michar71/DMX_CTRL/SW/Inc/WS2812B.h

#ifndef WS2812B_H
#define WS2812B_H

#include <stdio.h>
#include <string.h>
#include <stdarg.h>

// New version uses one large LUT as its faster index into sequential bytes for the GRB pattern
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
uint8_t rOffset;       // Index of red byte within each 3- or 4-byte pixel
uint8_t gOffset;       // Index of green byte
uint8_t bOffset;       // Index of blue byte

#endif // WS2812B_H
