michar71/DMX_CTRL/SW/Inc/serial_dmx_parser.h

/*
 * serial_dmx_parser.h
 *
 *  Created on: Apr 20, 2020
 *      Author: michael.hartmann
 */

#ifndef SERIAL_DMX_PARSER_H_
#define SERIAL_DMX_PARSER_H_

#include <stdio.h>
#include <string.h>
#include <stdarg.h>

void dmx_serial_process(void);

#endif /* SERIAL_DMX_PARSER_H_ */
