michar71/DMX_CTRL/SW/Inc/fx_install.h

/*
 * fx_install.h
 *
 *  Created on: Apr 15, 2020
 *      Author: Micha
 */

#ifndef FX_INSTALL_H_
#define FX_INSTALL_H_

//FX Includes
#include "fx_pwm_running_light.h"
#include "fx_pwm_pulsing_light.h"

void fx_install(void)
{
	//REGISTER FX HERE !!!
    fx_pwm_running_light();
    fx_pwm_running_pulse_light();
    fx_pwm_pulsing_light();
    fx_pwm_pulsing_pulse_light();
}

#endif /* FX_INSTALL_H_ */
