michar71/DMX_CTRL/SW/Inc/testmode.h

/*
 * testmode.h
 *
 *  Created on: Mar 6, 2020
 *      Author: Michael Hartmann
 */

#ifndef TESTMODE_H_
#define TESTMODE_H_

#include <stdint.h>

uint8_t process_testmode(void);

#endif /* TESTMODE_H_ */
